pozsarzs/mm4a/cad_files/connecting/connecting.sch

## KiCad design cad_files/connecting/connecting.sch (2019-09-29)

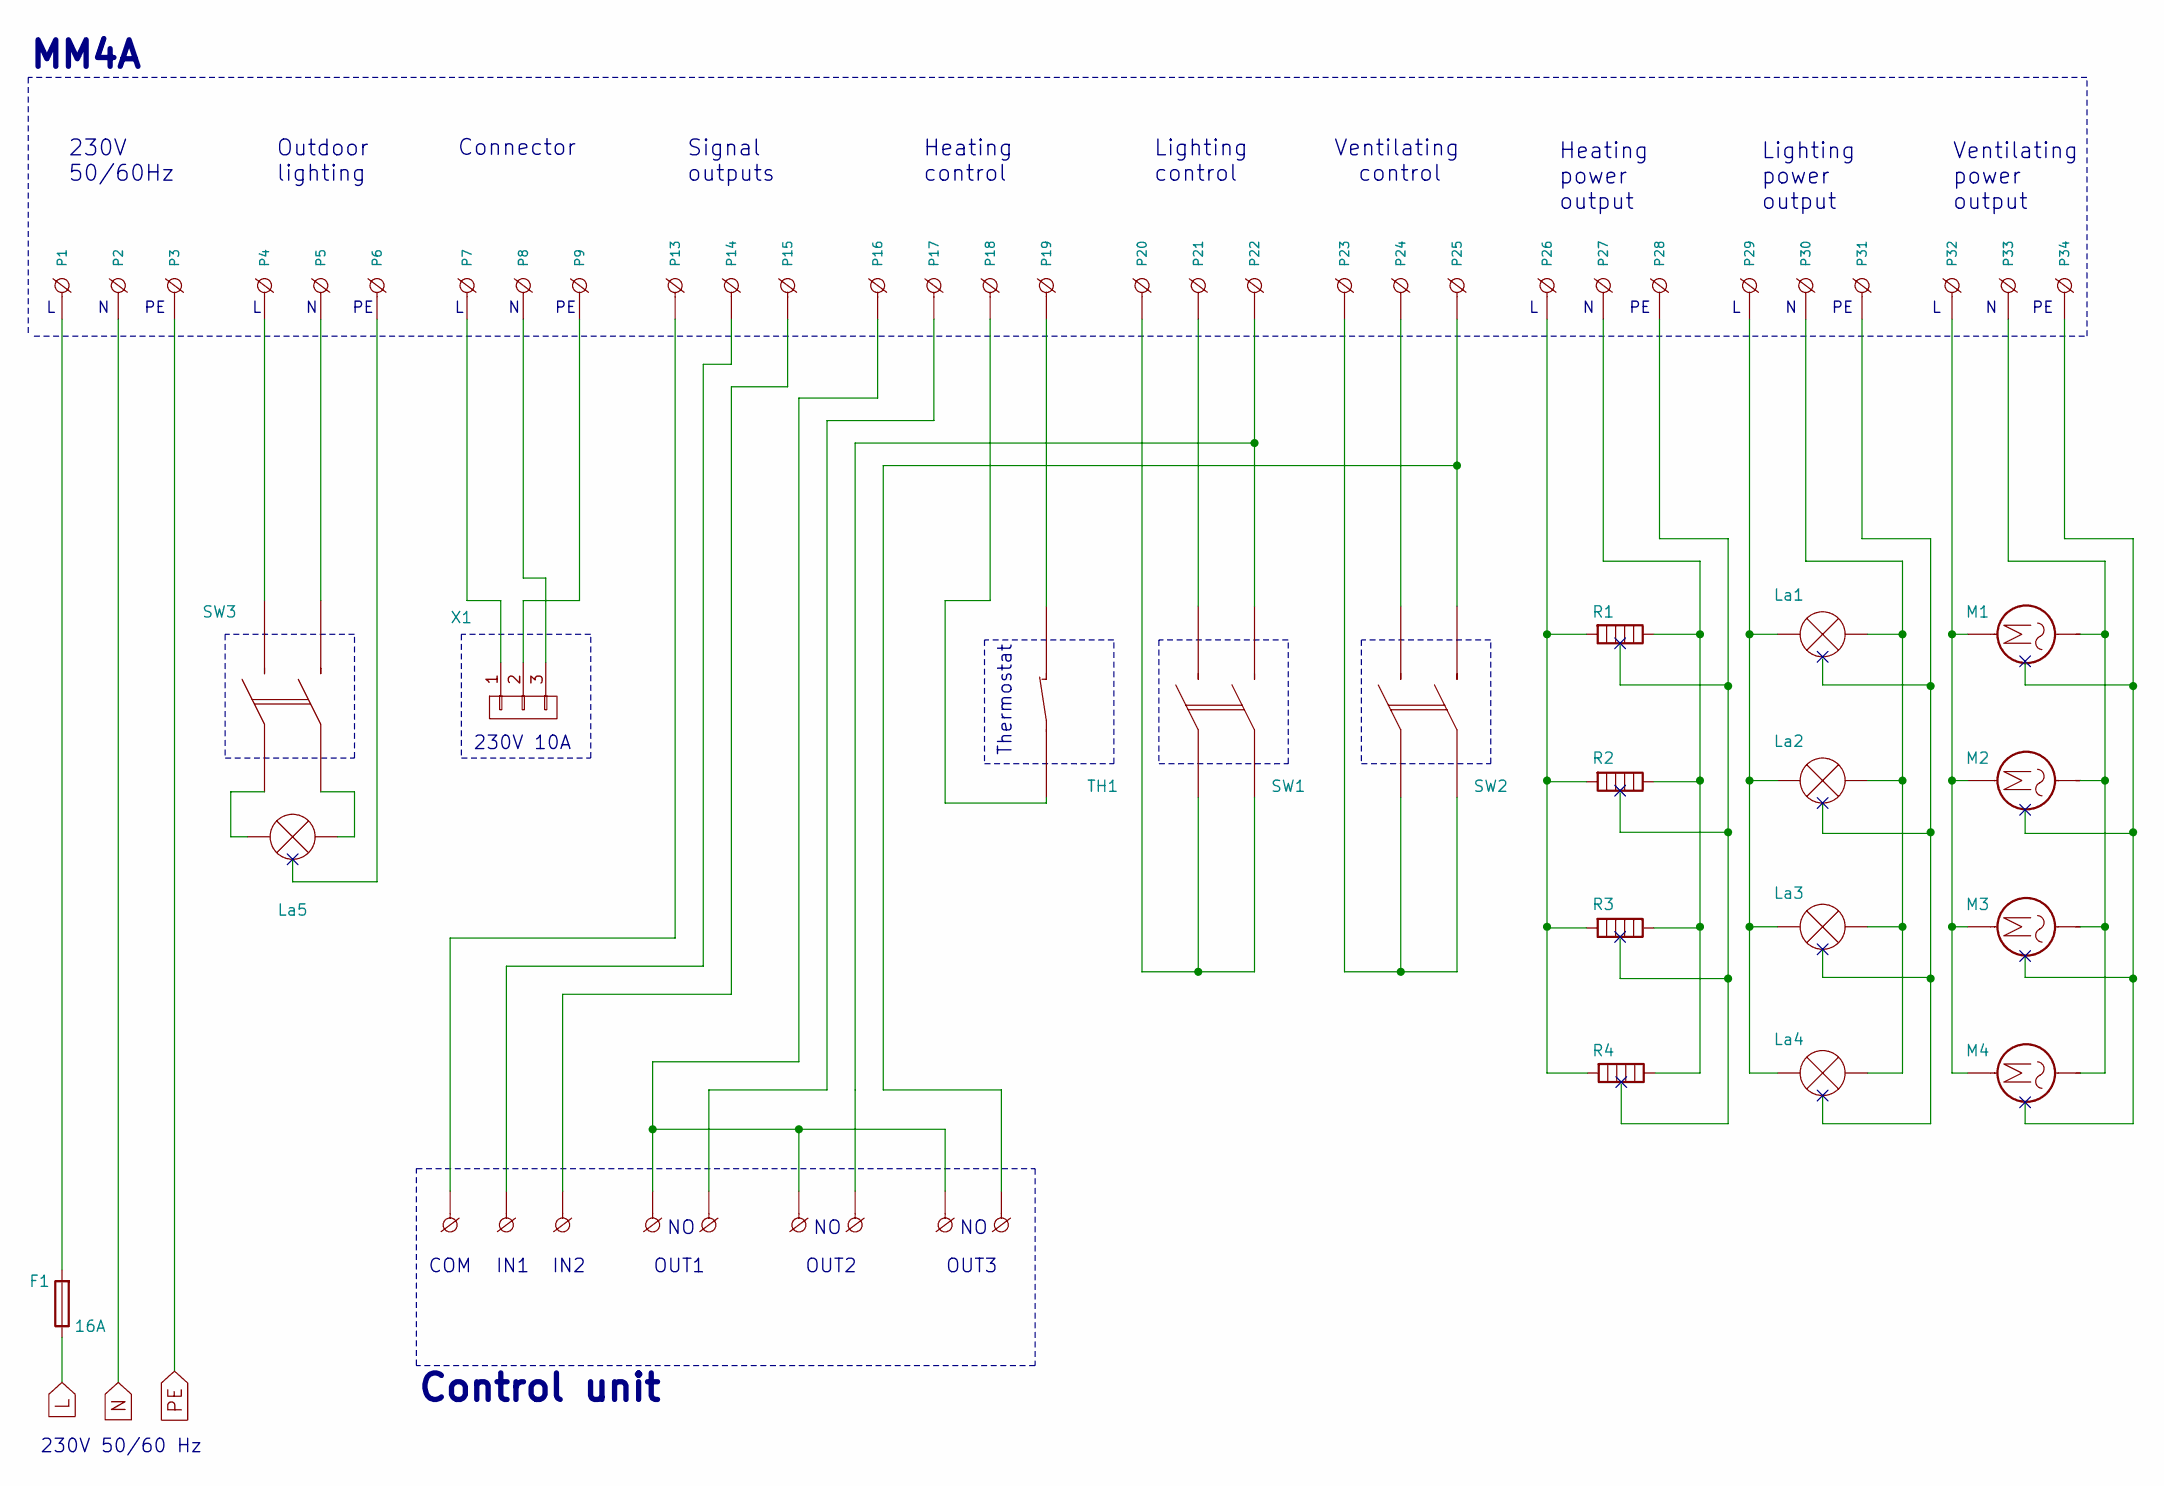
[picture p16: schematic connecting.sch]

Parts:
F1: 16A
La1, La2, La3, La4, La5: 230V; lamp
M1, M2, M3, M4: Motor_AC
P1, P2, P3, P4, P5, P6, P7, P8, P9, P13, P14, P15, P16, P17, P18, P19, P20, P21, P22, P23, P24, P25, P26, P27, P28, P29, P30, P31, P32, P33, P34: SCREW_CONN_1
R1, R2, R3, R4: Heater
SW1, SW2, SW3: SWITCH_2P
TH1: SWITCH_1P_CLOSED
X1: CONN_01X03

Connections:
L: F1.1
N: P2.1
unnamed: F1.2, P1.1
unnamed: La1.1 (-), La2.1 (-), La3.1 (-), La4.1 (-), P29.1
unnamed: La1.2 (+), La2.2 (+), La3.2 (+), La4.2 (+), P30.1
unnamed: La5.1 (-), SW3.1
unnamed: La5.2 (+), SW3.1
unnamed: M1.~, M2.~, M3.~, M4.~, P32.1, P33.1
unnamed: P4.1, SW3.2
unnamed: P5.1, SW3.2
unnamed: P7.1, X1.1
unnamed: P8.1, X1.3
unnamed: P9.1, X1.2
unnamed: P18.1, TH1.1
unnamed: P19.1, TH1.2
unnamed: P20.1, SW1.1
unnamed: P21.1, SW1.2
unnamed: P22.1, SW1.2
unnamed: P23.1, SW2.1
unnamed: P24.1, SW2.2
unnamed: P25.1, SW2.2
unnamed: P26.1, R1.2, R4.2
unnamed: P27.1, R1.1, R4.1
PE: P3.1

Notes on the sheet:
Heating power output
Ventilating power output
Lighting power output
Heating control
Ventilating control
Lighting control
Signal outputs
Connector
Outdoor lighting
230V 50/60Hz
MM4A
230V 50/60 Hz
COM
IN1
IN2
OUT1
OUT2
OUT3
Control unit
Thermostat
230V 10A
