pozsarzs/mm4a/cad_files/mm4a/mm4a.sch

## KiCad design cad_files/mm4a/mm4a.sch (2019-09-29)

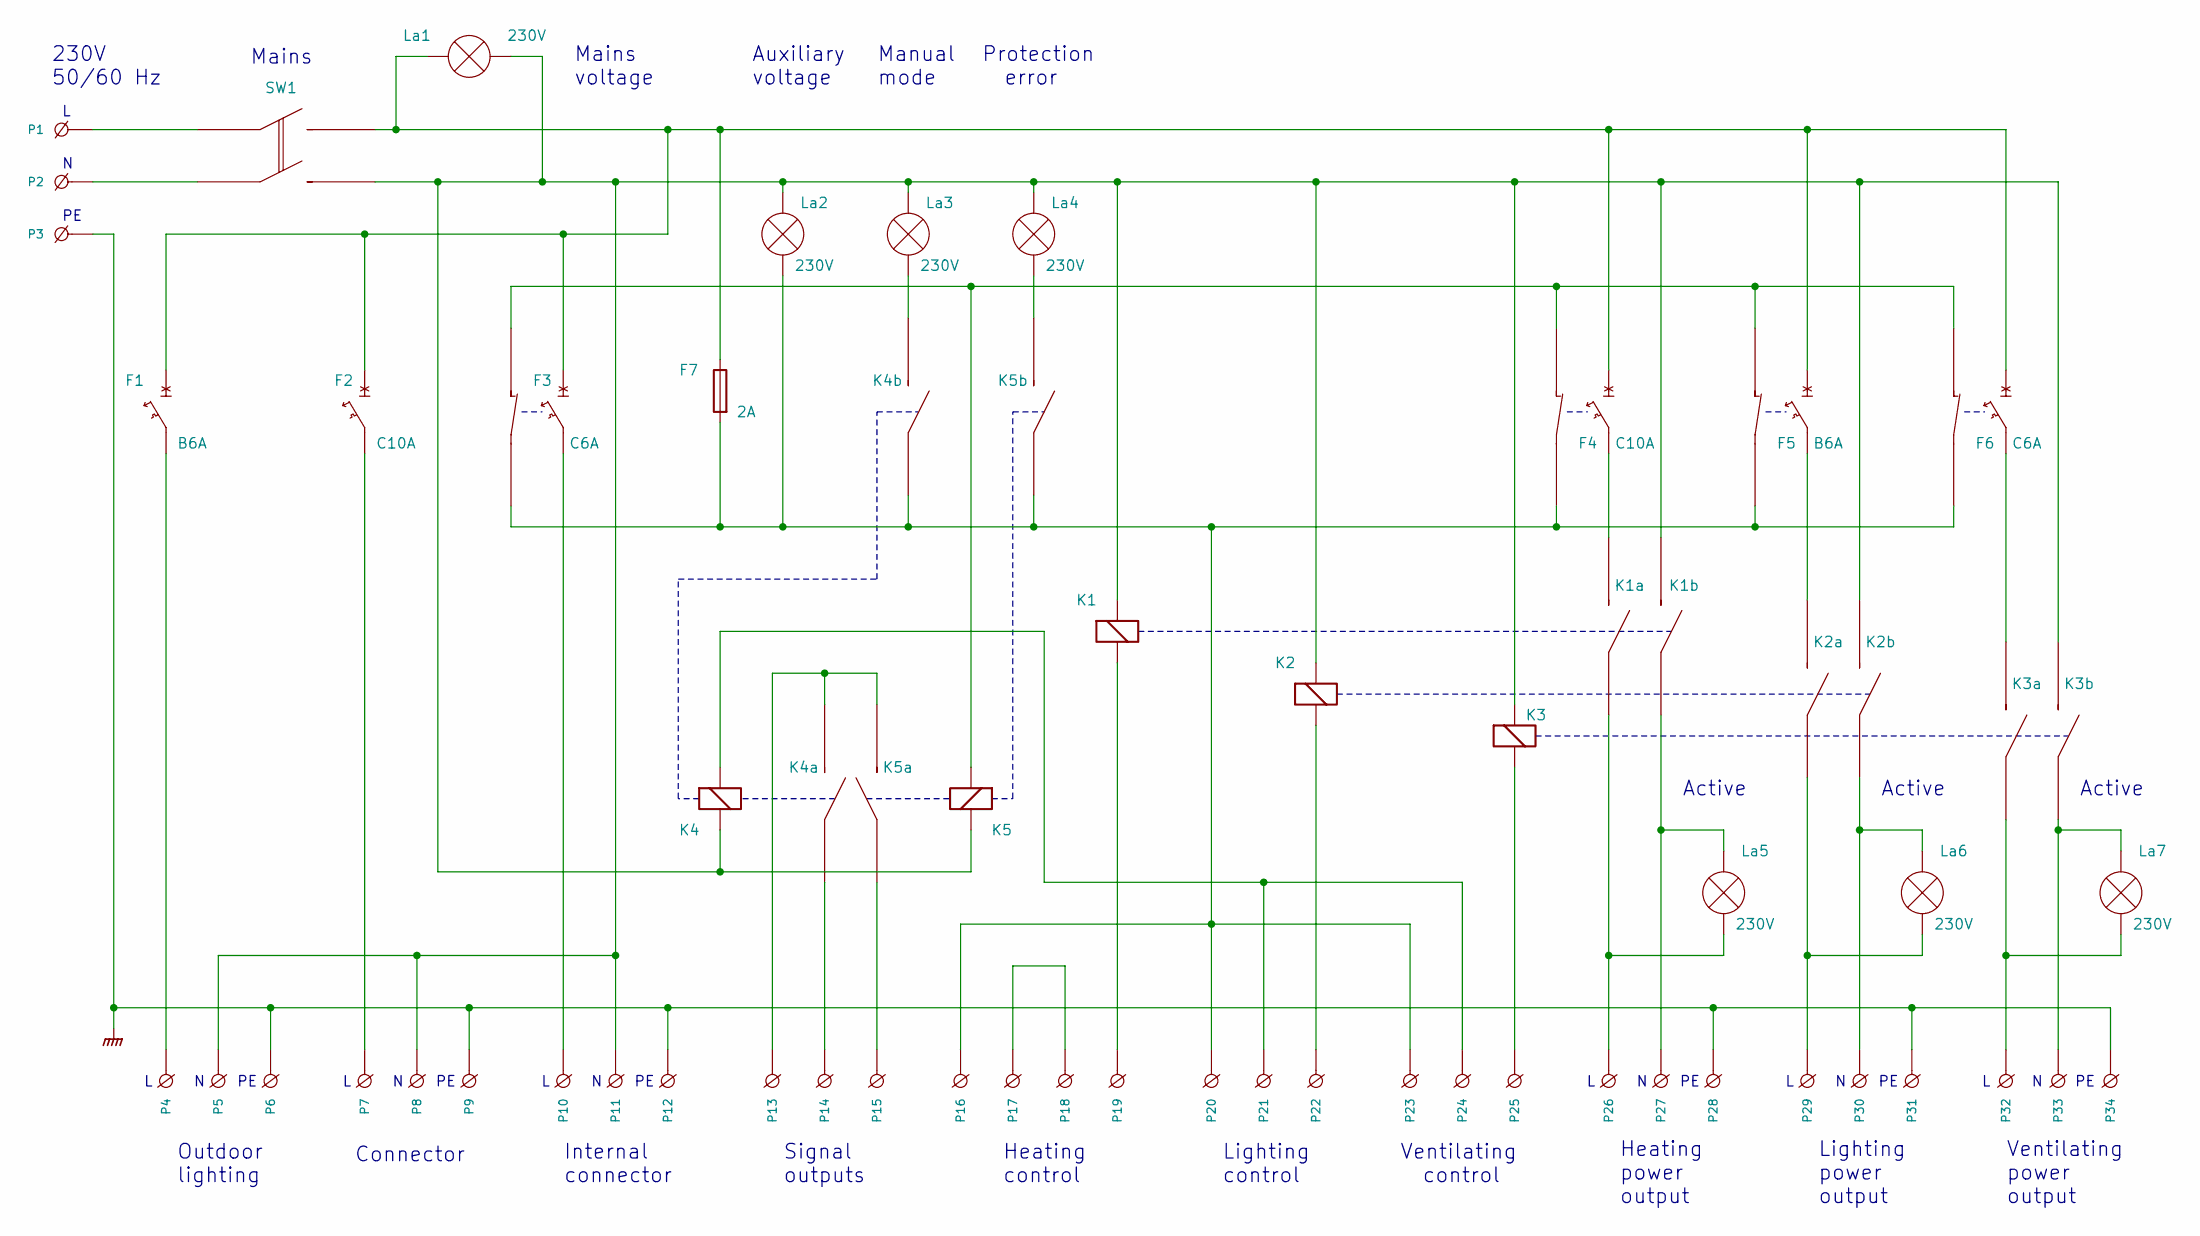
[picture p17: schematic mm4a.sch]

Parts:
ECB1, ECB2, ECB3, ECB4: SWITCH_1P_CLOSED
F1, F5: B6A
F2, F4: C10A
F3, F6: C6A
F7: 2A
K1, K2, K3, K4, K5: Electromagnetic_Actor
K1a, K1b, K2a, K2b, K3a, K3b, K4a, K4b, K5a, K5b: SWITCH_1P
La1, La2, La3, La4, La5, La6, La7: 230V; lamp
P1, P2, P3, P4, P5, P6, P7, P8, P9, P10, P11, P12, P13, P14, P15, P16, P17, P18, P19, P20, P21, P22, P23, P24, P25, P26, P27, P28, P29, P30, P31, P32, P33, P34: SCREW_CONN_1
SW1: SWITCH_2P

Connections:
GNDPWR: P3.1, P6.1, P9.1, P12.1, P28.1, P31.1, P34.1
unnamed: ECB1.1, ECB2.1, ECB3.1, ECB4.1, F7.2, K4b.1, K5b.1, La2.2 (+), P16.1, P20.1, P23.1
unnamed: ECB1.2, ECB2.2, ECB3.2, ECB4.2, K5.1 (-)
unnamed: F1.~, F2.~, F3.~, F4.~, F5.~, F6.~, F7.1, La1.1 (-), P4.1, SW1.2
unnamed: F2.~, P7.1
unnamed: F3.~, P10.1
unnamed: F4.~, K1a.2
unnamed: F5.~, K2a.2
unnamed: F6.~, K3a.2
unnamed: K1.1 (-), K1b.2, K2.1 (-), K2b.2, K3.1 (-), K3b.2, K4.2 (+), K5.2 (+), La1.2 (+), La2.1 (-), La3.1 (-), La4.1 (-), P5.1, P8.1, P11.1, SW1.2
unnamed: K1.2 (+), P19.1
unnamed: K1a.1, La5.1 (-), P26.1
unnamed: K1b.1, La5.2 (+), P27.1
unnamed: K2.2 (+), P22.1
unnamed: K2a.1, La6.1 (-), P29.1
unnamed: K2b.1, La6.2 (+), P30.1
unnamed: K3.2 (+), P25.1
unnamed: K3a.1, La7.1 (-), P32.1
unnamed: K3b.1, La7.2 (+), P33.1
unnamed: K4.1 (-), P21.1, P24.1
unnamed: K4a.1, P14.1
unnamed: K4a.2, K5a.2, P13.1
unnamed: K4b.2, La3.2 (+)
unnamed: K5a.1, P15.1
unnamed: K5b.2, La4.2 (+)
unnamed: P1.1, SW1.1
unnamed: P2.1, SW1.1
unnamed: P17.1, P18.1

Notes on the sheet:
Heating power output
Ventilating power output
Lighting power output
Heating control
Ventilating control
Lighting control
Internal connector
Signal outputs
Connector
Outdoor lighting
Auxiliary voltage
Manual mode
Protection error
Mains voltage
Mains
Active
230V 50/60 Hz
